lhaijun/MX_IMU/Hardware/component_library/model_3d/switch/Same_Sky_TS04-66-55-BK-100-SMT.step

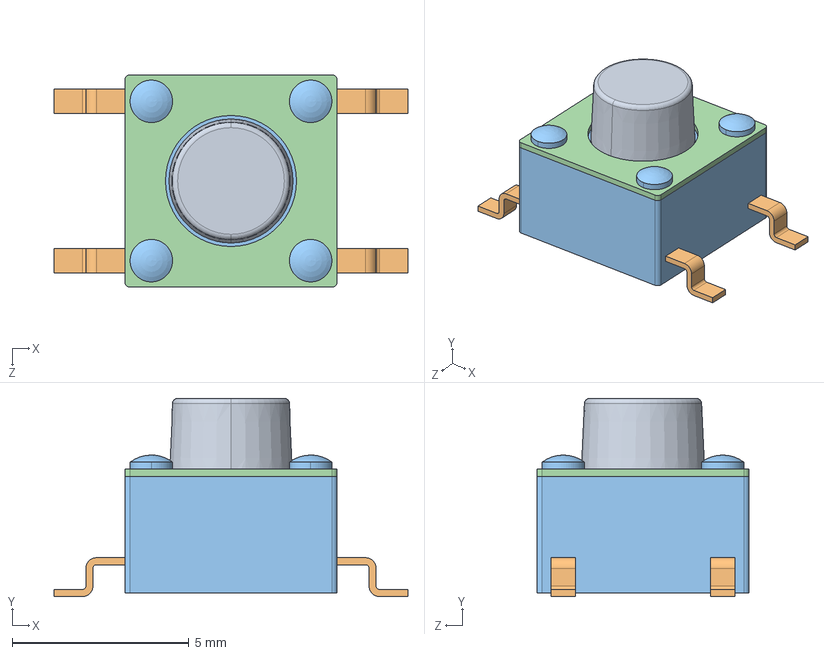
[picture p15: CAD file, 2025-06-17]
Hardware/component_library/model_3d/switch/Same_Sky_TS04-66-55-BK-100-SMT.step
10.0 x 5.60 x 6.00 mm
