lhaijun/MX_IMU/Hardware/component_library/model_3d/ti_buck/TPSM843x20.step

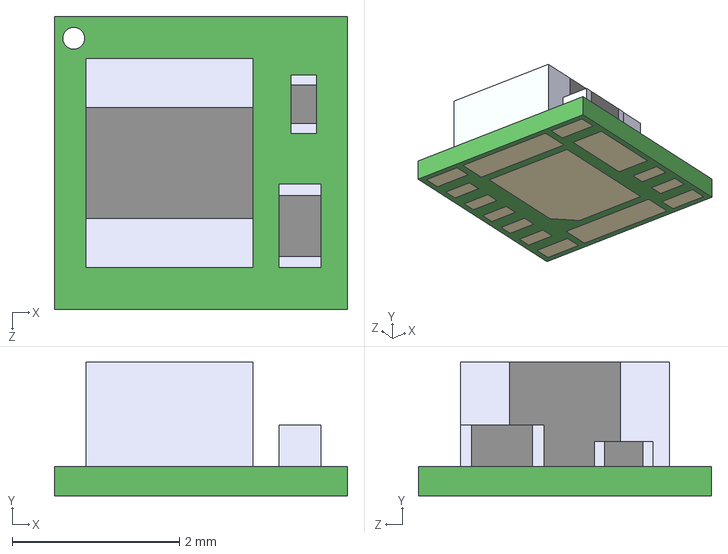
[picture p16: CAD file, 2025-06-17]
Hardware/component_library/model_3d/ti_buck/TPSM843x20.step
3.50 x 1.60 x 3.50 mm
