lhaijun/MX_IMU/Hardware/component_library/model_3d/ublox/SAM_AP214.STEP

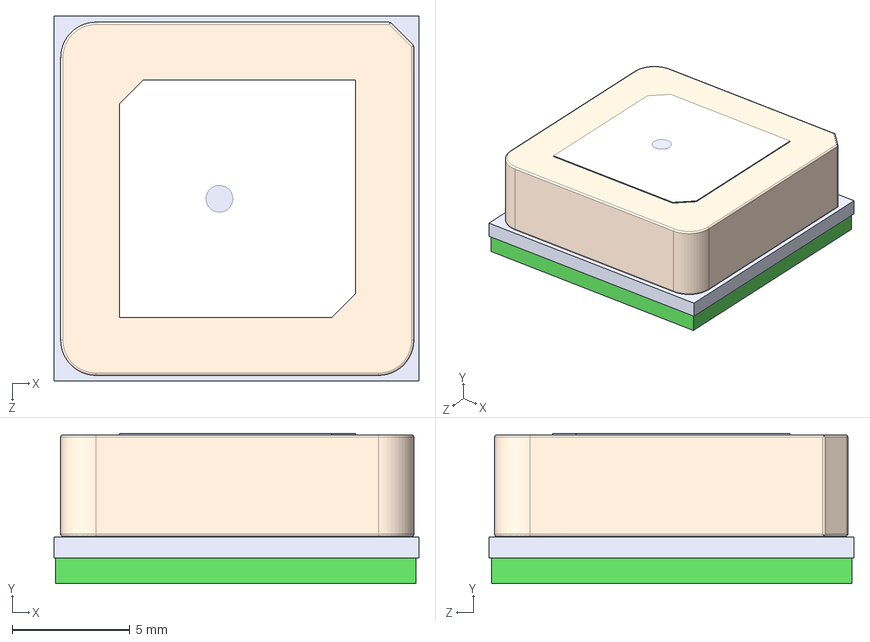
[picture p17: CAD file, 2025-06-17]
Hardware/component_library/model_3d/ublox/SAM_AP214.STEP
15.5 x 6.38 x 15.5 mm
Sam cavity
SAM PCB
SAM ANT
