lhaijun/MX_IMU/Hardware/component_library/RT9013-33GB.step

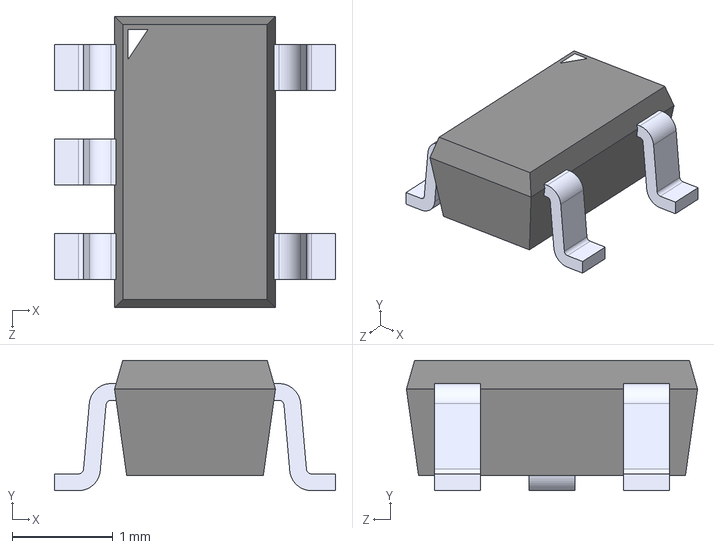
[picture p18: CAD file, 2025-06-17]
Hardware/component_library/RT9013-33GB.step
2.79 x 1.30 x 2.90 mm
