lhaijun/MX_IMU/Hardware/component_library/model_3d/0_standard/SOT-23-THN.stp

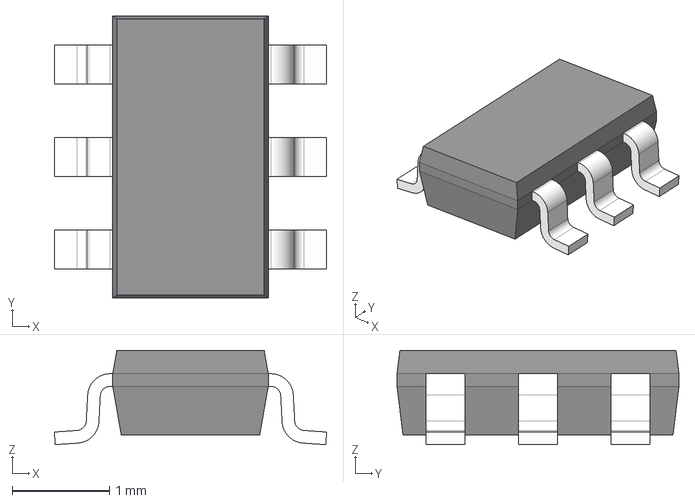
[picture p19: CAD file, 2025-06-17]
Hardware/component_library/model_3d/0_standard/SOT-23-THN.stp
2.80 x 2.90 x 0.97 mm
BODY-SOT
LEAD-SOT x 6
