lhaijun/MX_IMU/Hardware/component_library/model_3d/adafruit/4754 BNO085 STEMMA QT.step

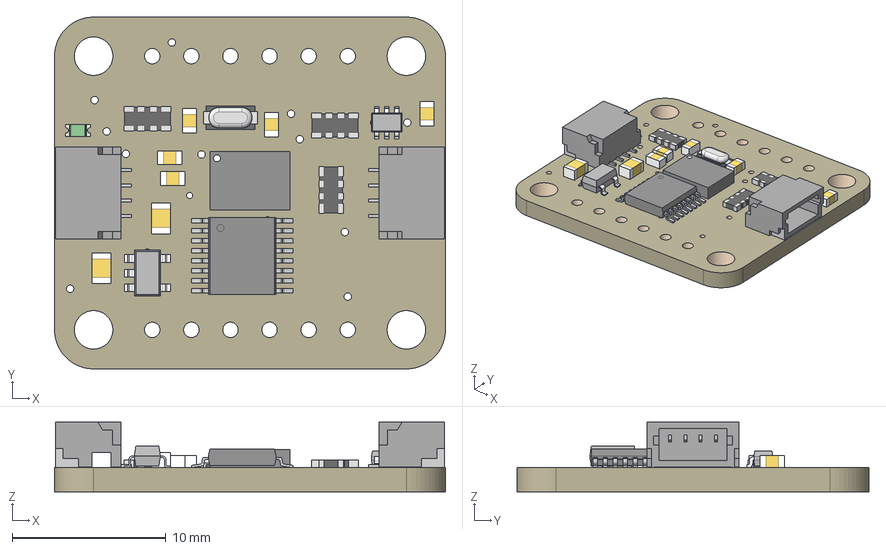
[picture p20: CAD file, 2025-06-17]
Hardware/component_library/model_3d/adafruit/4754 BNO085 STEMMA QT.step
25.4 x 22.9 x 4.53 mm
Board
10uF x 2
AP2112K-3.3
22pF x 5
10K x 3
BSS138
STEMMA_I2C_QT x 2
GREEN
BNO080
74AHC4050
