lhaijun/MX_IMU/Hardware/component_library/model_3d/digi_xbee/XBPro-whip.STEP

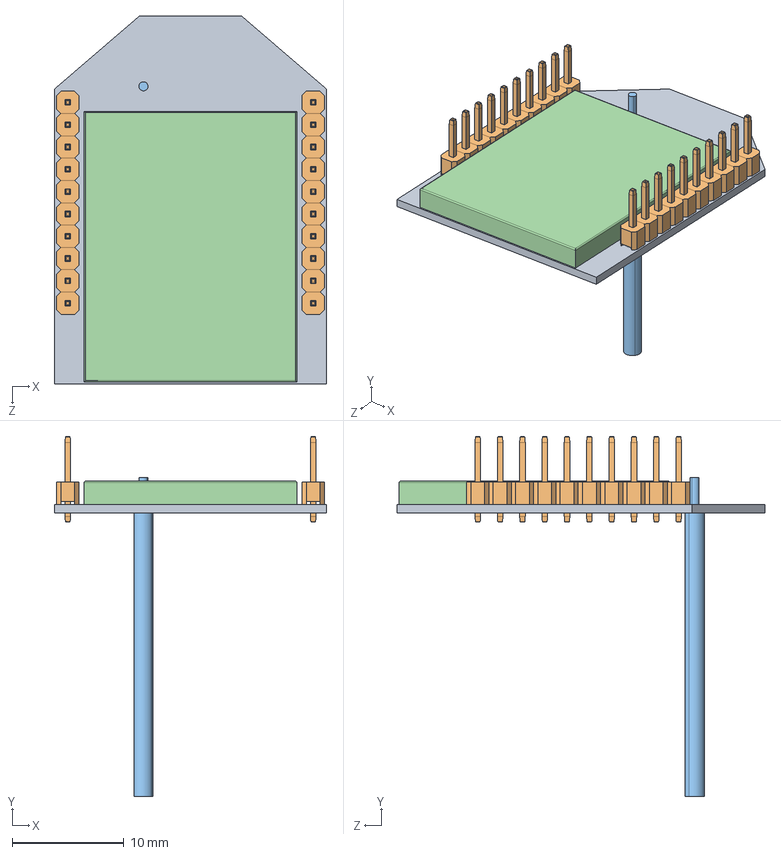
[picture p21: CAD file, 2025-06-17]
Hardware/component_library/model_3d/digi_xbee/XBPro-whip.STEP
24.4 x 32.3 x 32.9 mm
XBP24_with_Pads
2mmHeaderPin_straight x 20
1001557A
XBPro_shield
