lhaijun/MX_IMU/Hardware/component_library/model_3d/gct/BF030-16A-B1-0600-0277-0600-LB.STEP

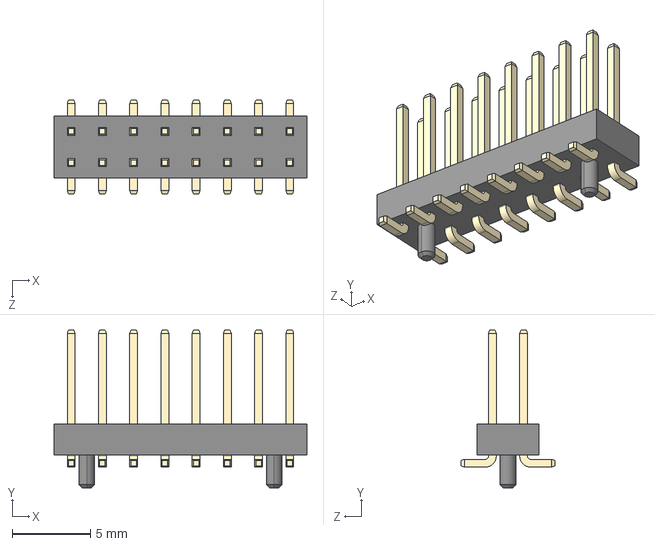
[picture p22: CAD file, 2025-06-17]
Hardware/component_library/model_3d/gct/BF030-16A-B1-0600-0277-0600-LB.STEP
16.2 x 10.1 x 6.00 mm
body^BF030-xxxx_16
pin^BF030-xxxx x 8
