lhaijun/MX_IMU/Hardware/component_library/model_3d/nxp/SOT782-1 HVSON-8.stp

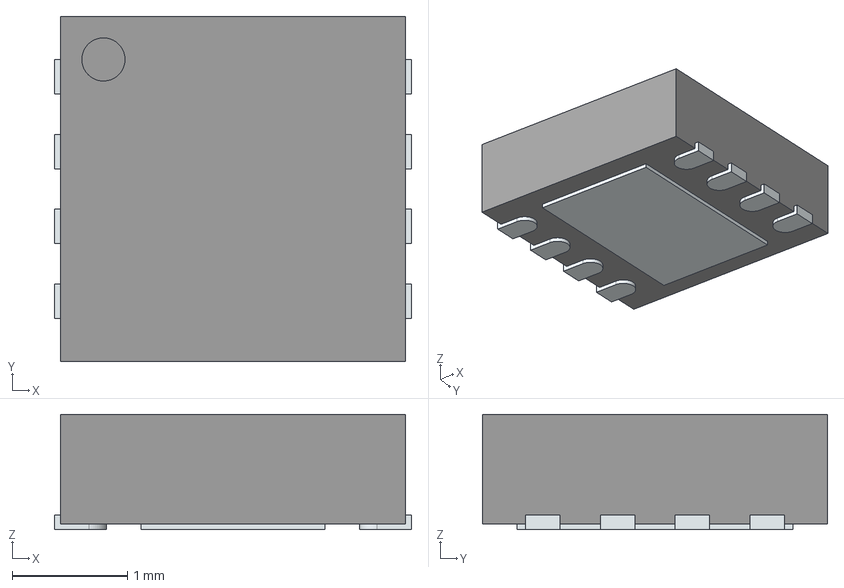
[picture p23: CAD file, 2025-06-17]
Hardware/component_library/model_3d/nxp/SOT782-1 HVSON-8.stp
3.10 x 3.00 x 1.00 mm
ThermalPin
PinsArrayLR
