lhaijun/MX_IMU/Hardware/component_library/model_3d/ti_buck/TPSM8290x.step

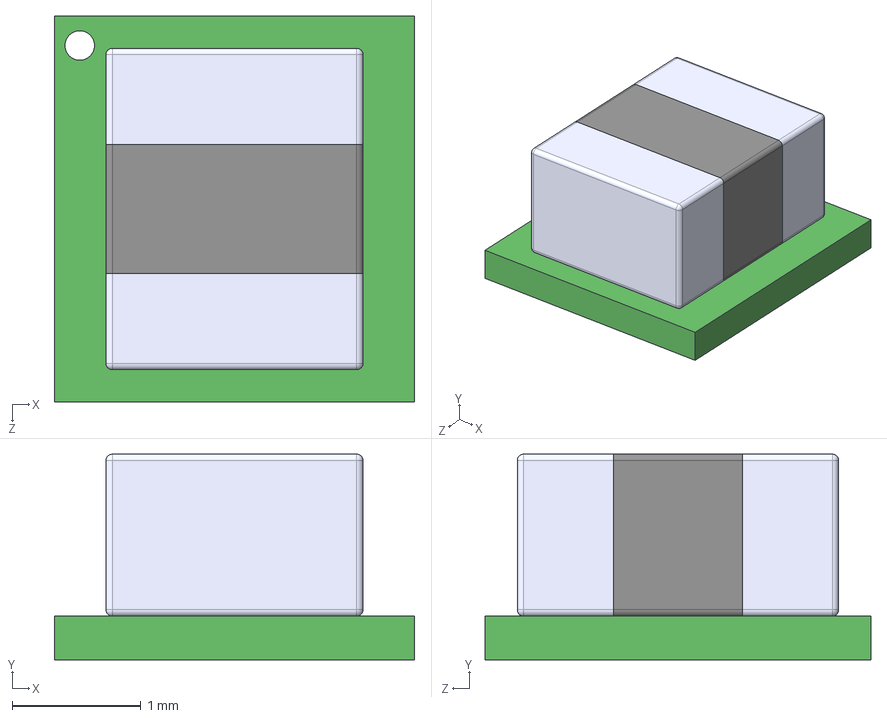
[picture p24: CAD file, 2025-06-17]
Hardware/component_library/model_3d/ti_buck/TPSM8290x.step
2.80 x 1.60 x 3.00 mm
