lhaijun/MX_IMU/Hardware/component_library/model_3d/adafruit/5396 Adafruit VL53L4CD.step

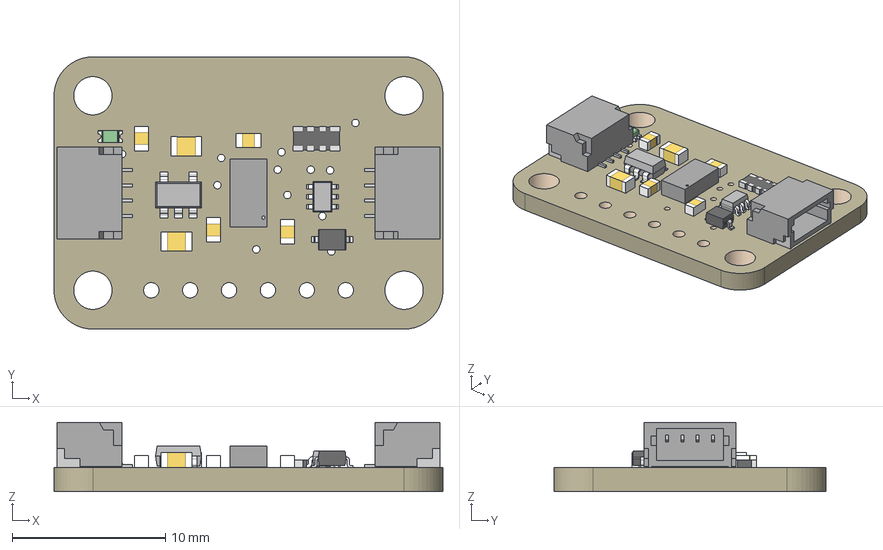
[picture p25: CAD file, 2025-06-17]
Hardware/component_library/model_3d/adafruit/5396 Adafruit VL53L4CD.step
25.4 x 17.8 x 4.53 mm
Board
VL53L0X
1N4148
10uF x 2
LP5907-2.8
10K x 4
10K_1
BSS138
STEMMA_I2C_QT x 2
GREEN
