lhaijun/MX_IMU/Hardware/component_library/model_3d/common/TXB0104QPWRQ1.step

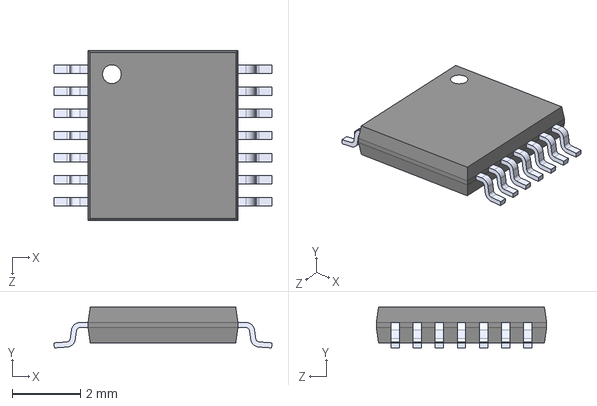
[picture p26: CAD file, 2025-06-17]
Hardware/component_library/model_3d/common/TXB0104QPWRQ1.step
6.40 x 1.20 x 5.00 mm
