lhaijun/MX_IMU/Hardware/component_library/model_3d/gct/BF080-16-A-1-L-C.STEP

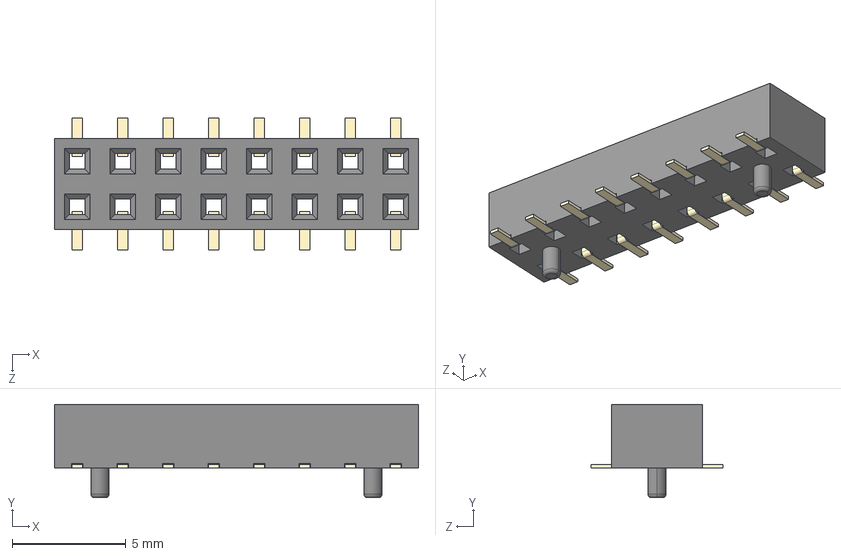
[picture p28: CAD file, 2025-06-17]
Hardware/component_library/model_3d/gct/BF080-16-A-1-L-C.STEP
16.0 x 4.10 x 5.80 mm
Pin gold x 8
