lhaijun/MX_IMU/Hardware/component_library/model_3d/adafruit/4682 Micro SD Breakout.step

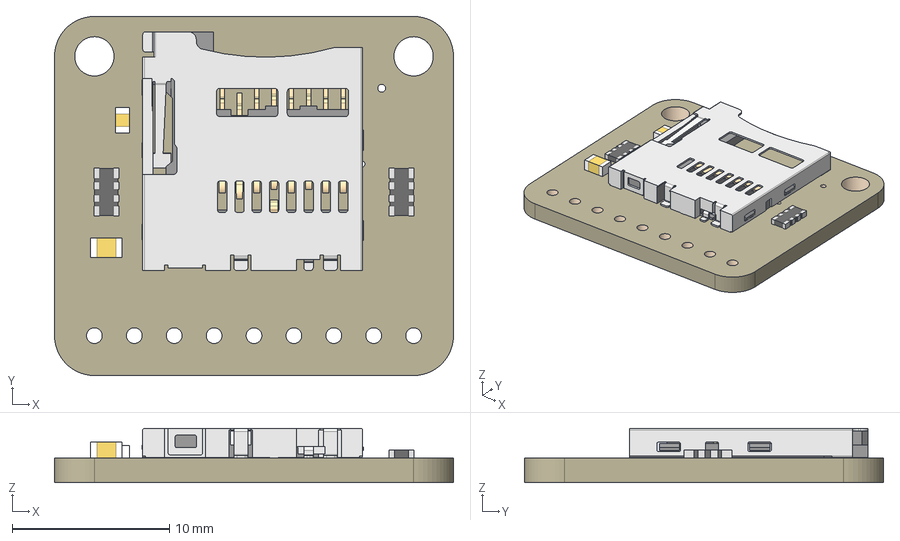
[picture p29: CAD file, 2025-06-17]
Hardware/component_library/model_3d/adafruit/4682 Micro SD Breakout.step
25.4 x 22.9 x 3.45 mm
Board
microSD
10uF
0.1uF
47K x 2
