lhaijun/MX_IMU/Hardware/component_library/model_3d/common/ecs_ecx-64.step

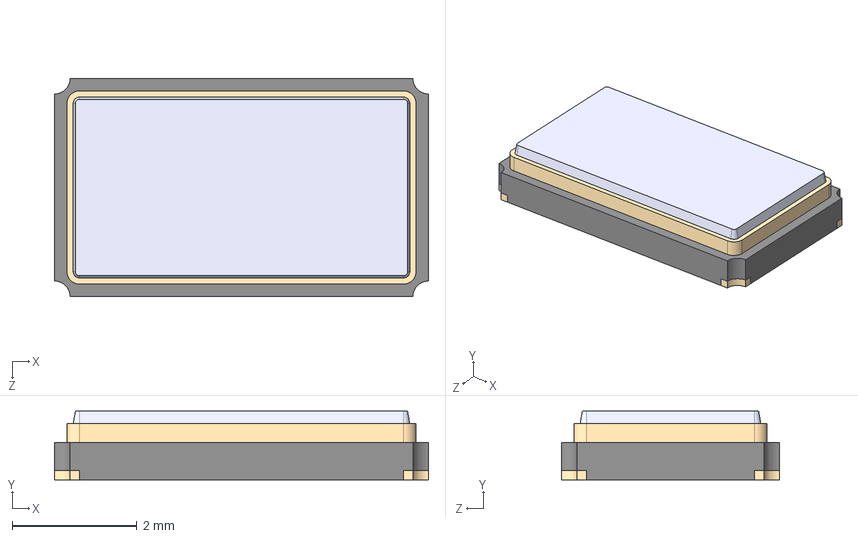
[picture p31: CAD file, 2025-06-17]
Hardware/component_library/model_3d/common/ecs_ecx-64.step
6.00 x 1.10 x 3.50 mm
