lhaijun/MX_IMU/Hardware/component_library/model_3d/gct/BF030-20A-B1-0360-0277-0600-LB.STEP

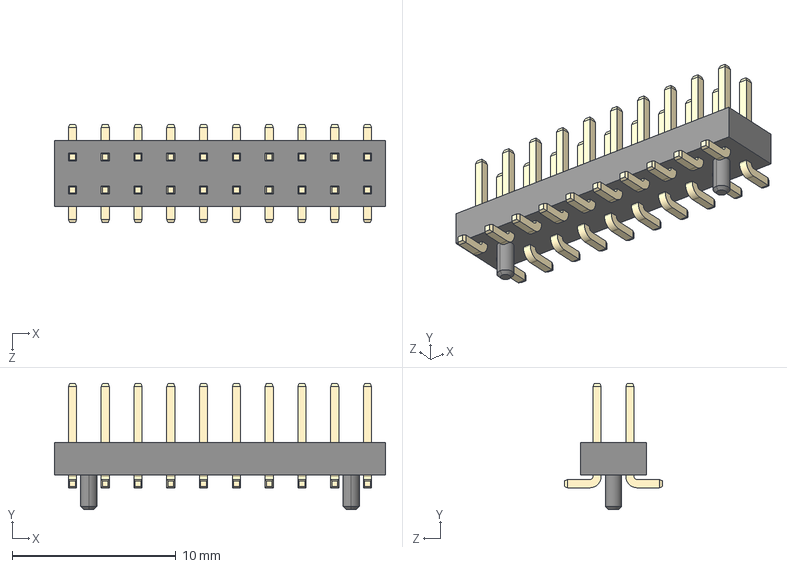
[picture p32: CAD file, 2025-06-17]
Hardware/component_library/model_3d/gct/BF030-20A-B1-0360-0277-0600-LB.STEP
20.2 x 7.70 x 6.00 mm
body^BF030-xxxx_20
pin^BF030-xxxx x 10
