lhaijun/MX_IMU/Hardware/component_library/model_3d/common/ecs_ecx-34r.step

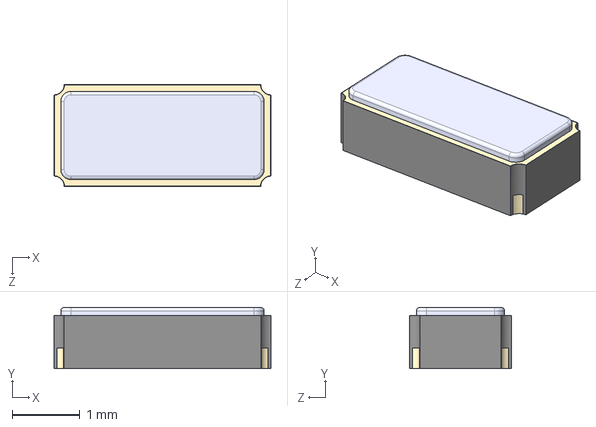
[picture p33: CAD file, 2025-06-17]
Hardware/component_library/model_3d/common/ecs_ecx-34r.step
3.20 x 0.9 x 1.50 mm
