lhaijun/MX_IMU/Hardware/component_library/model_3d/common/ECS-2520MV-080-BN-TR.step

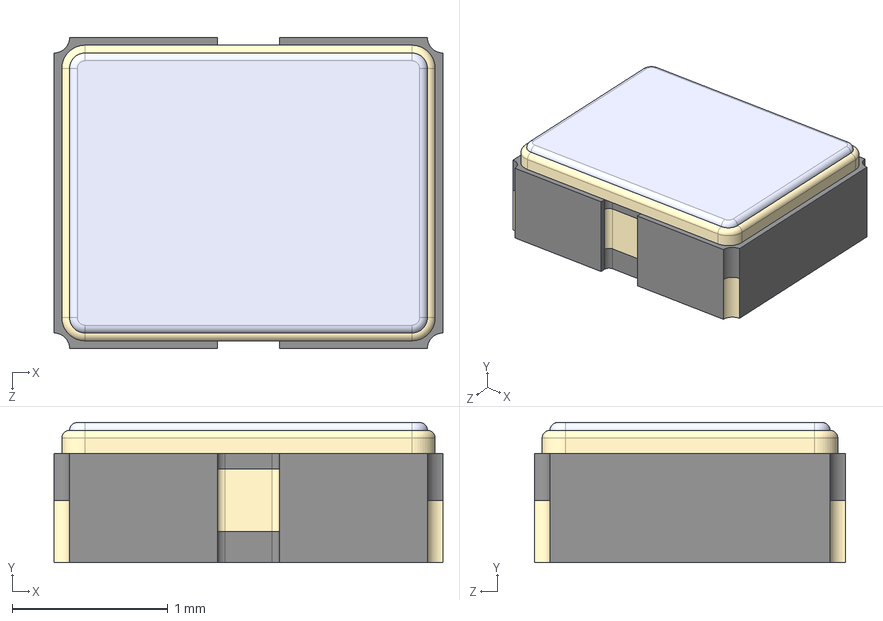
[picture p35: CAD file, 2025-06-17]
Hardware/component_library/model_3d/common/ECS-2520MV-080-BN-TR.step
2.50 x 0.9 x 2.00 mm
