lhaijun/MX_IMU/Hardware/component_library/model_3d/common/TXB0106RGYR.STEP

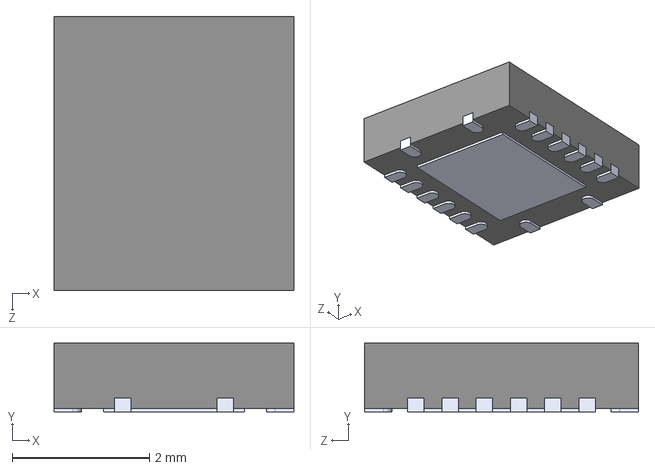
[picture p38: CAD file, 2025-06-17]
Hardware/component_library/model_3d/common/TXB0106RGYR.STEP
3.50 x 1.00 x 4.00 mm
